satomm1/EE256Project/software/ESP32Code/WiFi/SmartPotHTML.h

/*


  OK, ya ready for some fun? HTML + CSS styling + javascript all in and undebuggable environment

  one trick I've learned to how to debug HTML and CSS code.

  get all your HTML code (from html to /html) and past it into this test site
  muck with the HTML and CSS code until it's what you want
  https://www.w3schools.com/html/tryit.asp?filename=tryhtml_intro

  No clue how to debug javascrip other that write, compile, upload, refresh, guess, repeat

  I'm using class designators to set styles and id's for data updating
  for example:
  the CSS class .tabledata defines with the cell will look like
  <td><div class="tabledata" id = "switch"></div></td>

  the XML code will update the data where id = "switch"
  java script then uses getElementById
  document.getElementById("switch").innerHTML="Switch is OFF";


  .. now you can have the class define the look AND the class update the content, but you will then need
  a class for every data field that must be updated, here's what that will look like
  <td><div class="switch"></div></td>

  the XML code will update the data where class = "switch"
  java script then uses getElementsByClassName
  document.getElementsByClassName("switch")[0].style.color=text_color;


  the main general sections of a web page are the following and used here

  <html>
    <style>
    // dump CSS style stuff in here
    </style>
    <body>
      <header>
      // put header code for cute banners here
      </header>
      <main>
      // the buld of your web page contents
      </main>
      <footer>
      // put cute footer (c) 2021 xyz inc type thing
      </footer>
    </body>
    <script>
    // you java code between these tags
    </script>
  </html>


*/

// note R"KEYWORD( html page code )KEYWORD"; 
// again I hate strings, so char is it and this method let's us write naturally

const char PAGE_MAIN[] PROGMEM = R"=====(

<!DOCTYPE html>
<html lang="en" class="js-focus-visible">

<title>Smart Pot Web Display</title>

  <style>
    table {
      position: relative;
      width:100%;
      border-spacing: 0px;
    }
    tr {
      border: 1px solid white;
      font-family: "Verdana", "Arial", sans-serif;
      font-size: 20px;
    }
    th {
      height: 20px;
      padding: 3px 15px;
      background-color: #343a40;
      color: #FFFFFF !important;
      }
    td {
      height: 20px;
       padding: 3px 15px;
    }
    .tabledata {
      font-size: 24px;
      position: relative;
      padding-left: 5px;
      padding-top: 5px;
      height:   25px;
      border-radius: 5px;
      color: #FFFFFF;
      line-height: 20px;
      transition: all 200ms ease-in-out;
      background-color: #00AA00;
    }
    .bodytext {
      font-family: "Verdana", "Arial", sans-serif;
      font-size: 24px;
      text-align: left;
      font-weight: light;
      border-radius: 5px;
      display:inline;
    }
    .navbar {
      width: 100%;
      height: 50px;
      margin: 0;
      padding: 10px 0px;
      background-color: #FFF;
      color: #000000;
      border-bottom: 5px solid #293578;
    }
    .fixed-top {
      position: fixed;
      top: 0;
      right: 0;
      left: 0;
      z-index: 1030;
    }
    .navtitle {
      float: left;
      height: 50px;
      font-family: "Verdana", "Arial", sans-serif;
      font-size: 50px;
      font-weight: bold;
      line-height: 50px;
      padding-left: 20px;
    }
   .navheading {
     position: fixed;
     left: 60%;
     height: 50px;
     font-family: "Verdana", "Arial", sans-serif;
     font-size: 20px;
     font-weight: bold;
     line-height: 20px;
     padding-right: 20px;
   }
   .navdata {
      justify-content: flex-end;
      position: fixed;
      left: 70%;
      height: 50px;
      font-family: "Verdana", "Arial", sans-serif;
      font-size: 20px;
      font-weight: bold;
      line-height: 20px;
      padding-right: 20px;
   }
    .category {
      font-family: "Verdana", "Arial", sans-serif;
      font-weight: bold;
      font-size: 32px;
      line-height: 50px;
      padding: 20px 10px 0px 10px;
      color: #000000;
    }
    .heading {
      font-family: "Verdana", "Arial", sans-serif;
      font-weight: normal;
      font-size: 28px;
      text-align: left;
    }
  
    .btn {
      background-color: #767676;
      border: none;
      color: white;
      padding: 10px 20px;
      text-align: center;
      text-decoration: none;
      display: inline-block;
      font-size: 16px;
      margin: 4px 2px;
      cursor: pointer;
    }

    .btn2 {
      background-color: #444444;
      border: none;
      color: white;
      padding: 10px 20px;
      text-align: center;
      text-decoration: none;
      display: inline-block;
      font-size: 16px;
      margin: 4px 2px;
      cursor: pointer;
    }

    .foot {
      font-family: "Verdana", "Arial", sans-serif;
      font-size: 20px;
      position: relative;
      height:   30px;
      text-align: center;   
      color: #AAAAAA;
      line-height: 20px;
    }
    .container {
      max-width: 1800px;
      margin: 0 auto;
    }
    table tr:first-child th:first-child {
      border-top-left-radius: 5px;
    }
    table tr:first-child th:last-child {
      border-top-right-radius: 5px;
    }
    table tr:last-child td:first-child {
      border-bottom-left-radius: 5px;
    }
    table tr:last-child td:last-child {
      border-bottom-right-radius: 5px;
    }
    
  </style>

  <body style="background-color: #efefef" onload="process()">
  
    <header>
      <div class="navbar fixed-top">
          <div class="container">
            <div class="navtitle">Smart Pot</div>
            <div class="navdata" id = "date">mm/dd/yyyy</div>
            <div class="navheading">DATE</div><br>
            <div class="navdata" id = "time">00:00:00</div>
            <div class="navheading">TIME</div>
          </div>
      </div>
    </header>
  
    <main class="container" style="margin-top:70px">
      <div class="category">Sensor Readings</div>
      <div style="border-radius: 10px !important;">
      <table style="width:75%">
      <colgroup>
        <col span="1" style="background-color:rgb(230,230,230); width: 40%; color:#000000 ;">
        <col span="1" style="background-color:rgb(200,200,200); width: 30%; color:#000000 ;">
      </colgroup>
      <col span="2"style="background-color:rgb(0,0,0); color:#FFFFFF">
      <col span="2"style="background-color:rgb(0,0,0); color:#FFFFFF">
      <tr>
        <th colspan="1"><div class="heading">Sensor</div></th>
        <th colspan="1"><div class="heading">Value</div></th>
      </tr>
      <tr>
        <td><div class="bodytext" id = "temperature_title">Temperature (&deg;C)</div></td>
        <td><div class="tabledata" id = "temperature"></div></td>
      </tr>
      <tr>
        <td><div class="bodytext" id = "soil_title">Soil Moisture (%), threshold = 20%</div></td>
        <td><div class="tabledata" id = "soil_moisture"></div></td>
      </tr>
      </table>
    </div>
    <br>

    <div class="category">Controls</div>
    <div class="bodytext">Water The Plant </div>
    <button type="button" class = "btn" id = "btn_water" onclick="WATER_BUTTON()">Activate Pump</button>
    </div>
    <br>
    <div class="bodytext">Water Level Threshold </div>
    <button type="button" class = "btn2" id = "btn_low" onclick="LOW_THRESHOLD_BUTTON()">Low</button>
    <button type="button" class = "btn" id = "btn_high" onclick="HIGH_THRESHOLD_BUTTON()">High</button>
    </div>
    <br>
    <div class="bodytext">Units</div>
    <button type="button" class = "btn" id = "btn_fahrenheit" onclick="FAHRENHEIT_BUTTON()">Fahrenheit</button>
    <button type="button" class = "btn2" id = "btn_celsius" onclick="CELSIUS_BUTTON()">Celsius</button>
    </div>
    <br>
    <br>

  </main>

  <footer div class="foot" id = "temp" >EE256 Final Project 2023, Matthew Sato</div></footer>
  
  </body>


  <script type = "text/javascript">
  
    // global variable visible to all java functions
    var xmlHttp=createXmlHttpObject();

    // function to create XML object
    function createXmlHttpObject(){
      if(window.XMLHttpRequest){
        xmlHttp=new XMLHttpRequest();
      }
      else{
        xmlHttp=new ActiveXObject("Microsoft.XMLHTTP");
      }
      return xmlHttp;
    }

    // handles button press by sending processing string back to server
    function WATER_BUTTON() {
      var xhttp = new XMLHttpRequest();        
      xhttp.open("PUT", "WATER_BUTTON", false);
      xhttp.send();
    }

    // handles button press by sending processing string back to server
    function LOW_THRESHOLD_BUTTON() {
      document.getElementById("soil_title").innerHTML="Soil Moisture (%), threshold = 20%";
      document.getElementById("btn_low").style.backgroundColor="#444444";
      document.getElementById("btn_high").style.backgroundColor="#767676";
      var xhttp = new XMLHttpRequest(); 
      xhttp.open("PUT", "LOW_THRESHOLD_BUTTON", false);
      xhttp.send(); 
    }

    // handles button press by sending processing string back to server
    function HIGH_THRESHOLD_BUTTON() {
      document.getElementById("soil_title").innerHTML="Soil Moisture (%), threshold = 30%";
      document.getElementById("btn_low").style.backgroundColor="#767676";
      document.getElementById("btn_high").style.backgroundColor="#444444";
      var xhttp = new XMLHttpRequest(); 
      xhttp.open("PUT", "HIGH_THRESHOLD_BUTTON", false);
      xhttp.send(); 
    }

    // handles button press by sending processing string back to server
    function FAHRENHEIT_BUTTON() {
      document.getElementById("temperature_title").innerHTML="Temperature (&deg;F)";
      document.getElementById("btn_fahrenheit").style.backgroundColor="#444444";
      document.getElementById("btn_celsius").style.backgroundColor="#767676";
      var xhttp = new XMLHttpRequest(); 
      xhttp.open("PUT", "FAHRENHEIT_BUTTON", false);
      xhttp.send(); 
    }

    // handles button press by sending processing string back to server
    function CELSIUS_BUTTON() {
      document.getElementById("temperature_title").innerHTML="Temperature (&deg;C)";
      document.getElementById("btn_fahrenheit").style.backgroundColor="#767676";
      document.getElementById("btn_celsius").style.backgroundColor="#444444";
      var xhttp = new XMLHttpRequest(); 
      xhttp.open("PUT", "CELSIUS_BUTTON", false);
      xhttp.send(); 
    }

    // function to handle the response from the ESP
    function response(){
      var message;
      var barwidth;
      var currentsensor;
      var xmlResponse;
      var xmldoc;
      var dt = new Date();
      var color = "#e8e8e8";
     
      // get the xml stream
      xmlResponse=xmlHttp.responseXML;
  
      // get host date and time
      document.getElementById("time").innerHTML = dt.toLocaleTimeString();
      document.getElementById("date").innerHTML = dt.toLocaleDateString();
  
      // Temperature
      xmldoc = xmlResponse.getElementsByTagName("TEMP"); // temperature value
      message = xmldoc[0].firstChild.nodeValue;      

    //   color = "#0000aa";     
      barwidth = message;
      document.getElementById("temperature").innerHTML=message;
      document.getElementById("temperature").style.width=(barwidth+"%");
      // if you want to use global color set above in <style> section
      // other wise uncomment and let the value dictate the color
      //document.getElementById("temperature").style.backgroundColor=color;
      //document.getElementById("temperature").style.borderRadius="5px";
        
      // Soil Moisture
      xmldoc = xmlResponse.getElementsByTagName("SOIL");
      message = xmldoc[0].firstChild.nodeValue;

    //   color = "#0000aa";
      document.getElementById("soil_moisture").innerHTML=message;
      width = message;
      document.getElementById("soil_moisture").style.width=(width+"%");
      // document.getElementById("soil_moisture").style.backgroundColor=color;
      //document.getElementById("soil_moisture").style.backgroundColor=color;
      //document.getElementById("soil_moisture").style.borderRadius="5px";
      
      
      xmldoc = xmlResponse.getElementsByTagName("Unit");
      message = xmldoc[0].firstChild.nodeValue;
  
      // Change color of Units buttons based on what is selected
      if (message == "2") {
        document.getElementById("temperature_title").innerHTML="Temperature (&deg;F)";
        document.getElementById("btn_fahrenheit").style.backgroundColor="#444444";
        document.getElementById("btn_celsius").style.backgroundColor="#767676";
      }
      else if (message == "1") {
        document.getElementById("temperature_title").innerHTML="Temperature (&deg;C)";
        document.getElementById("btn_fahrenheit").style.backgroundColor="#767676";
        document.getElementById("btn_celsius").style.backgroundColor="#444444";
      }
         
      xmldoc = xmlResponse.getElementsByTagName("Water_Level");
      message = xmldoc[0].firstChild.nodeValue;
      // Change color of Units buttons based on what is selected
      if (message == 1){
        document.getElementById("soil_title").innerHTML="Soil Moisture (%), threshold = 20%";
        document.getElementById("btn_low").style.backgroundColor="#444444";
        document.getElementById("btn_high").style.backgroundColor="#767676";
      }
      else if (message == 2) {
        document.getElementById("soil_title").innerHTML="Soil Moisture (%), threshold = 30%";
        document.getElementById("btn_low").style.backgroundColor="#767676";
        document.getElementById("btn_high").style.backgroundColor="#444444";
      }
     }

    // general processing code for the web page to ask for an XML steam
    // this is actually why you need to keep sending data to the page to 
    // force this call with stuff like this
    // server.on("/xml", SendXML);
    // otherwise the page will not request XML from the ESP, and updates will not happen
    function process(){
     
     if(xmlHttp.readyState==0 || xmlHttp.readyState==4) {
        xmlHttp.open("PUT","xml",true);
        xmlHttp.onreadystatechange=response;
        xmlHttp.send(null);
      }       
        // you may have to play with this value, big pages need more porcessing time, and hence
        // a longer timeout
        setTimeout("process()",100);
    }
  
  
  </script>

</html>



)=====";
