satomm1/EE256Project/software/PIC32Code/ProjectSource/EventCheckers.c

/****************************************************************************
 Module
   EventCheckers.c

 Revision
   1.0.1

 Description
   This is the sample for writing event checkers along with the event
   checkers used in the basic framework test harness.

 Notes
   Note the use of static variables in sample event checker to detect
   ONLY transitions.

 History
 When           Who     What/Why
 -------------- ---     --------
 08/06/13 13:36 jec     initial version
****************************************************************************/

// this will pull in the symbolic definitions for events, which we will want
// to post in response to detecting events
#include "ES_Configure.h"
// This gets us the prototype for ES_PostAll
#include "ES_Framework.h"
// this will get us the structure definition for events, which we will need
// in order to post events in response to detecting events
#include "ES_Events.h"
// if you want to use distribution lists then you need those function
// definitions too.
#include "ES_PostList.h"
// This include will pull in all of the headers from the service modules
// providing the prototypes for all of the post functions
#include "ES_ServiceHeaders.h"
// this test harness for the framework references the serial routines that
// are defined in ES_Port.c
#include "ES_Port.h"
// include our own prototypes to insure consistency between header &
// actual functionsdefinition
#include "EventCheckers.h"
#include "dbprintf.h"

static uint8_t UserButtonStatus;
static uint8_t WaterButtonStatus;

/****************************************************************************
 Function
   Check4Keystroke
 Parameters
   None
 Returns
   bool: true if a new key was detected & posted
 Description
   checks to see if a new key from the keyboard is detected and, if so,
   retrieves the key and posts an ES_NewKey event to TestHarnessService0
 Notes
   The functions that actually check the serial hardware for characters
   and retrieve them are assumed to be in ES_Port.c
   Since we always retrieve the keystroke when we detect it, thus clearing the
   hardware flag that indicates that a new key is ready this event checker
   will only generate events on the arrival of new characters, even though we
   do not internally keep track of the last keystroke that we retrieved.
 Author
   J. Edward Carryer, 08/06/13, 13:48
****************************************************************************/
bool Check4Keystroke(void)
{
  if (IsNewKeyReady())   // new key waiting?
  {
    ES_Event_t ThisEvent;
    ThisEvent.EventType   = ES_NEW_KEY;
    ThisEvent.EventParam  = GetNewKey();
    ES_PostAll(ThisEvent);
    return true;
  }
  return false;
}


void InitUserButton(void) 
{
    UserButtonStatus = PORTAbits.RA11;
}

bool CheckUserButton(void)
{
    bool ReturnVal = false;
    
    // Get current state of button
    uint8_t CurrentUserButtonStatus = PORTAbits.RA11;
    
    if (UserButtonStatus != CurrentUserButtonStatus) {
        // button state has changed
        ReturnVal = true;
        
        // Post the event of a button up or down
        ES_Event_t ThisEvent;
        if (CurrentUserButtonStatus == 1) { // Button is down
            ThisEvent.EventType = EV_USER_BUTTON_DOWN;
            PostUserButtonSM(ThisEvent);
        } else { // button is now up
            ThisEvent.EventType = EV_USER_BUTTON_UP;
            PostUserButtonSM(ThisEvent);
        }
        
        // update the last button state
        UserButtonStatus =  CurrentUserButtonStatus;
    }
    return ReturnVal;
}


void InitWaterButton(void) 
{
    WaterButtonStatus = PORTDbits.RD8;
}

bool CheckWaterButton(void)
{
    bool ReturnVal = false;
    
    // Get current state of button
    uint8_t CurrentWaterButtonStatus = PORTDbits.RD8;
    
    if (WaterButtonStatus != CurrentWaterButtonStatus) {
        // button state has changed
        ReturnVal = true;
        
        // Post the event of a button up or down
        ES_Event_t ThisEvent;
        if (CurrentWaterButtonStatus == 1) { // Button is down
            ThisEvent.EventType = EV_WATER_BUTTON_DOWN;
            PostWaterButtonSM(ThisEvent);
        } else { // button is now up
            ThisEvent.EventType = EV_WATER_BUTTON_UP;
            PostWaterButtonSM(ThisEvent);
        }
        
        // update the last button state
        WaterButtonStatus =  CurrentWaterButtonStatus;
    }
    return ReturnVal;
}
